stustanet/waschfreiheit/firmware/source/sensor/state_estimation.c

/*
 * Copyright 2018 Daniel Frejek
 * This source code is licensed under the MIT license that can be found
 * in the LICENSE file.
 */


#include "state_estimation.h"

#include <string.h>

#include "debug_assert.h"

static bool check_config(const state_estimation_params_t *params)
{
	for (uint8_t i = 0; i < SE_STATECOUNT; i++)
	{
		if (params->state_filter.window_sizes[i] > SE_MAX_WINDOW_SIZE ||
			params->state_filter.window_sizes[i] == 0)
		{
			printf("Invalid stateest window size %u\n", params->state_filter.window_sizes[i]);
			return false;
		}
	}

	if (params->input_filter.num_samples == 0)
	{
		printf("Number of lowpass samples must not be zero!\n");
		return false;
	}

	return true;
}


/*
 * Update the input filter.
 * This proceses the raw ADC values and calculates the <current> input filter value from the data.
 * <current> describes the short-time average power consumption of the measured device.
 * This also increments the current filter counter.
 */
static void update_input_filter(state_estimation_data_t *data, uint16_t value)
{
	ASSERT(value < (1 << 12));

	// sacle from 12 bit to 32 bit
	uint32_t value_scaled = value << 20;

	uint32_t absval = 0;

	if (value_scaled > data->input_filter.mid)
	{
		absval = value_scaled - data->input_filter.mid;
		data->input_filter.mid += data->params.input_filter.mid_value_adjustment_speed;
	}
	else if (value_scaled < data->input_filter.mid)
	{
		absval = data->input_filter.mid - value_scaled;
		data->input_filter.mid -= data->params.input_filter.mid_value_adjustment_speed;
	}

	// sacle from 32 bit to 18 bit
	absval = absval >> 14;

	data->input_filter.counter++;
	data->input_filter.current = (data->input_filter.current * data->params.input_filter.lowpass_weight + absval) / (data->params.input_filter.lowpass_weight + 1);
}


/*
 * Calculates the number of valid elements in the current window.
 *
 * NOTE:
 * The return value assumes that the element referenced by next_free already in use
 */
static uint16_t calc_current_window_used(const state_estimation_data_t *data)
{
	if (data->state_filter.window_oldest_valid > data->state_filter.window_next_free)
	{
		// Wrap-around
		// => valid values before next free and after oldest_valid
		return (data->state_filter.window_next_free + 1) + (SE_MAX_WINDOW_SIZE - data->state_filter.window_oldest_valid);
	}
	else
	{
		// Linear
		// => valid values between next free and oldest valid
		return (data->state_filter.window_next_free - data->state_filter.window_oldest_valid) + 1;
	}
}


/*
 * Adjust the window size to the current window size as defined by the current state.
 * If an old value that contributed to the <window_sum> falls out, it is subtracted from the sum.
 * Also, this function advances the window by one so that <window_next_free> will point to the next unused element
 */
static void adjust_window_size(state_estimation_data_t *data)
{
	ASSERT(data->state_filter.current_state < SE_STATECOUNT);

	// first adjust the window size so that at least one new value fits in
	uint16_t current_wnd_size = data->params.state_filter.window_sizes[data->state_filter.current_state];
	uint16_t current_window_used = calc_current_window_used(data);

	uint16_t discard_idx = data->state_filter.window_oldest_valid;
	while (current_window_used >= current_wnd_size)
	{
		// discard value
		if (data->state_filter.window[discard_idx] & (0x8000))
		{
			// msb set -> this value was used
			// => subtract it from sum

			ASSERT(data->state_filter.window_sum >= (data->state_filter.window[discard_idx] & 0x7fff));

			data->state_filter.window_sum -= (data->state_filter.window[discard_idx] & 0x7fff);
		}

		current_window_used--;
		discard_idx = (discard_idx + 1) % SE_MAX_WINDOW_SIZE;
	}

	data->state_filter.window_oldest_valid = discard_idx;
	data->state_filter.window_next_free = (data->state_filter.window_next_free + 1) % SE_MAX_WINDOW_SIZE;

	ASSERT(data->state_filter.window_oldest_valid < SE_MAX_WINDOW_SIZE);
	ASSERT(data->state_filter.window_next_free < SE_MAX_WINDOW_SIZE);
}


/*
 * Adds the <current> input value to the window at <window_next_free> and updates the <window_sum>
 * according to the reject threshold/block filter.
 *
 * NOTE: After this function <window_next_free> will point to a used element!
 */
static void update_reject_thd_filter(state_estimation_data_t *data)
{
	// scale to 15 bit
	uint16_t currentval = data->input_filter.current >> 3;
	ASSERT(currentval < (1 << 15));

	uint16_t buffer_pos = data->state_filter.window_next_free;

	if (currentval > data->params.state_filter.reject_threshold)
	{
		/*
		 * Value is above threshold => Three possibilities
		 * I    Less than <reject_consec_count> consecutive values are above threshold
		 *      (<above_reject_counter> < <reject_consec_count>)
		 *      => Insert normally, increment <above_reject_counter>
		 * II   Exactly <reject_consec_count> consecutive values are above the threshold
		 *      => Insert and add <current> to sum (mark as used)
		 *      => Insert and add all not yet added old values to the sum (and mark all as used)
		 * III  More than <reject_consec_count> consecutive values are above the threshold
		 *      => Insert and add <current> to sum (mark as used)
		 */


		if (data->state_filter.above_reject_counter >= data->params.state_filter.reject_consec_count)
		{
			// II or III => Insert and add <current> to sum (and mark as used)
			data->state_filter.window_sum += currentval;
			data->state_filter.window[buffer_pos] = currentval | (0x8000);

			if (data->state_filter.above_reject_counter == data->params.state_filter.reject_consec_count)
			{
				// II => add all old values to sum (and mark as added)

				ASSERT(data->params.state_filter.reject_consec_count <= calc_current_window_used(data));

				for (uint16_t i = 0; i < data->params.state_filter.reject_consec_count; i++)
				{
					if (buffer_pos > 0)
					{
						buffer_pos--;
					}
					else
					{
						buffer_pos = SE_MAX_WINDOW_SIZE - 1;
					}

					// Must not be added yet
					ASSERT((data->state_filter.window[buffer_pos] & 0x8000) == 0);

					data->state_filter.window_sum += data->state_filter.window[buffer_pos];
					data->state_filter.window[buffer_pos] |= 0x8000; // mark as used (contributed to sum)
				}

				// Max value -> directly accept next value
				data->state_filter.above_reject_counter = 0xffff;
			}
			return;
		}
		else
		{
			// I => only increment counter
			data->state_filter.above_reject_counter++;
		}
	}
	else
	{
		/*
		 * Value is below threshold
		 * => Only need to reset the counter
		 */
		data->state_filter.above_reject_counter = 0;
	}

	// add 15 bit scaled value (without "contributed" tag)
	data->state_filter.window[buffer_pos] = currentval;
}


/*
 * Updates / changes the current state according to the transition matrix and the old state
 * Also check the end state timer.
 */
static void do_state_transition(state_estimation_data_t *data)
{
	ASSERT(data->state_filter.current_state < SE_STATECOUNT);

	/*
	 * This is the offset of the state transition values for the current state
	 */
	uint8_t row_offset = data->state_filter.current_state * (SE_STATECOUNT - 1);

	int16_t average = stateest_get_current_rf_value(data);

	ASSERT(average >= 0);


	for (uint8_t i = 0; i < SE_STATECOUNT; i++)
	{
		uint16_t lookup_idx;

		if (i < data->state_filter.current_state)
		{
			// Index < current -> lookup at i
			lookup_idx = i;
		}
		else if(data->state_filter.current_state == i)
		{
			// i is current state -> skip this, this column does not exist in the matrix
			continue;
		}
		else
		{
			// after the current state, look up at i - 1
			lookup_idx = i - 1;
		}

		int16_t v = data->params.state_filter.transition_matrix[row_offset + lookup_idx];

		if (v < 0)
		{
			// Switch to state i, if average < -v
			if (average < -v)
			{
				data->state_filter.current_state = i;
				break;
			}
		}
		else if (v > 0)
		{
			// Switch to state i, if average > v
			if (average > v)
			{
				data->state_filter.current_state = i;
				break;
			}
		}
	}

	// finally check max time condition for end state
	if (data->state_filter.current_state == SE_STATE_END)
	{
		data->state_filter.end_state_timer++;
		if (data->state_filter.end_state_timer > data->state_filter.max_end_state_time)
		{
			// Too long in end state => switch to OFF
			data->state_filter.end_state_timer = 0;
			data->state_filter.current_state = SE_STATE_OFF;
		}
	}
	else
	{
		data->state_filter.end_state_timer = 0;
	}
}


static void update_state_filter(state_estimation_data_t *data)
{
	adjust_window_size(data);
	update_reject_thd_filter(data);
	do_state_transition(data);
}


int stateest_init(state_estimation_data_t *data, const state_estimation_params_t *params, uint16_t adc_samples_per_sec)
{
	if (!check_config(params))
	{
		return 1;
	}

	// init data
	memcpy(&(data->params), params, sizeof(data->params));
	data->input_filter.mid = SE_INITIAL_MID_VALUE;
	data->input_filter.current = 0;
	data->input_filter.counter = 0;

	memset(data->state_filter.window, 0, sizeof(data->state_filter.window));
	data->state_filter.window_next_free = 0;
	data->state_filter.window_oldest_valid = 0;
	data->state_filter.end_state_timer = 0;
	data->state_filter.max_end_state_time = (uint16_t)(((uint32_t)SE_MAX_END_STATE_TIME) * adc_samples_per_sec / params->input_filter.num_samples);
	data->state_filter.above_reject_counter = 0;
	data->state_filter.window_sum = 0;
	data->state_filter.current_state = SE_STATE_OFF;

	stateest_set_adc_sps(data, adc_samples_per_sec);

	return 0;
}


void stateest_set_adc_sps(state_estimation_data_t *data, uint16_t adc_samples_per_sec)
{
	if (data->params.input_filter.num_samples == 0)
	{
		// not initialized
		return;
	}

	data->state_filter.end_state_timer = 0;
	data->state_filter.max_end_state_time = (uint16_t)(((uint32_t)SE_MAX_END_STATE_TIME) * adc_samples_per_sec / data->params.input_filter.num_samples);
}


state_update_result_t stateest_update(state_estimation_data_t *data, uint16_t raw_value)
{
	// First update the input filter
	update_input_filter(data, raw_value);

	if (data->input_filter.counter >= data->params.input_filter.num_samples)
	{
		// if <num_samples> valuess processed, update the state filter

		data->input_filter.counter = 0;

		// rememebr if the last state was an ON state
		uint8_t was_on = (data->state_filter.current_state >= SE_STATE_ON_THRESHOLD);

		// update the state
		update_state_filter(data);

		// was_on != is_on => notify caller
		if (was_on != (data->state_filter.current_state >= SE_STATE_ON_THRESHOLD))
		{
			if (was_on)
			{
				return state_update_changed_to_off;
			}
			return state_update_changed_to_on;
		}
	}

	// no frame or on state unchanged
	return state_update_unchanged;
}


uint32_t stateest_get_frame(const state_estimation_data_t *data)
{
	if (data->input_filter.counter == 0)
	{
		return data->input_filter.current >> 2;
	}
	else
	{
		return 0xffffffff;
	}
}


int16_t stateest_get_current_rf_value(const state_estimation_data_t *data)
{
	ASSERT(data->state_filter.current_state < SE_STATECOUNT);
	return data->state_filter.window_sum / calc_current_window_used(data);
}


bool stateest_check_config(const state_estimation_data_t *data)
{
	return check_config(&(data->params));
}
