stustanet/waschfreiheit/firmware/include/messagetypes.h

/*
 * Copyright 2018 Daniel Frejek
 * This source code is licensed under the MIT license that can be found
 * in the LICENSE file.
 */


/*
 * Structure definitions of the network messages.
 * The auth structures are defined in the auth module, the handshake
 * messages here only work as headers for the "real" handshake.
 */

#pragma once

#include <stdint.h>
#include <meshnw.h>
#include "state_estimation_params.h"

/*
 * Standard ACK codes
 * The ACK code is command specific, however, if the code is used to report an error,
 * the following codes sould be used.
 */
#define ACK_OK            0 /* OK */
#define ACK_WRONGSIZE     1 /* Unexpected message size */
#define ACK_BADINDEX      2 /* A specified channel index parameter is outside of the allowed range */
#define ACK_BADPARAM      3 /* Invalid (non-index) parameter */
#define ACK_NOTSUP        4 /* Unsupported action */
#define ACK_BADSTATE      5 /* Command rejected because of the current state */
#define ACK_RETRANSMIT 0x80 /* MSB is always set if the ack was sent twice */


typedef uint8_t msg_type_t;

/*
 * Part 1 of the auth handshake
 * master -> slave
 *
 * When this is sent by the master node, this also contains a temporary route
 * to the master node.
 *
 * NOTE: Anyone can send a valid HS1 even without knowing the key so this message
 *       should not change any configuration.
 */
#define MSG_TYPE_AUTH_HS_1                  1
typedef struct
{
	msg_type_t type;
	// The next hop used for the handshake reply
	nodeid_t reply_route;
} __attribute__((packed)) msg_auth_hs_1_t;


/*
 * Part 2 of the auth handshake
 * slave -> master
 * The HS2 is signed so the information from this message can be trusted.
 *
 * Some basic status information is packed into the hs2 message to reduce the overhead of a reconnect.
 */
#define MSG_TYPE_AUTH_HS_2                  2

#define MSG_HS_2_STATUS_ROUTES 1 /* [sensor -> master] Routes OK */
#define MSG_HS_2_STATUS_SENSOR 2 /* [sensor -> master] Sensors active */
typedef struct
{
	msg_type_t type;

	// Node status (MSG_HS_2_STATUS_*)
	uint8_t status;

	// Sensor channels with a high measurement
	uint16_t channels;
} __attribute__((packed)) msg_auth_hs_2_t;


/*
 * ACK packet for authenticated packets.
 * Only the slave of a connection sends ACK
 * result_code is a command-defined result value,
 *   if the msb is set, this is an retransmission-ack
 */
#define MSG_TYPE_AUTH_ACK                   3
typedef struct
{
	msg_type_t type;
	uint8_t result_code;
} __attribute__((packed)) msg_auth_ack_t;


/*
 * Clear all current routes and resets the node's state.
 * This is the first message expected by a node after the handshake.
 * This message must at least contain a route to the master.
 */
#define MSG_TYPE_ROUTE_RESET                4

/*
 * Just like ROUTE_RESET but old routes are kept
 */
#define MSG_TYPE_ROUTE_APPEND               5

/*
 * Data for both types of route messages.
 */
typedef struct
{
	msg_type_t type;
	// The next hop used for the handshake reply
	struct
	{
		nodeid_t dst;
		nodeid_t next;
	} r[1]; // at least one route, an empty table would make no sense
} __attribute__((packed)) msg_route_data_t;


/*
 * Configures a sensor channel
 */
#define MSG_TYPE_CONFIGURE_SENSOR_CHANNEL   6
typedef struct
{
	msg_type_t type;
	uint8_t channel_id;
	state_estimation_params_t params;
} __attribute__((packed)) msg_configure_sensor_t;


/*
 * Command to the node to establish the status connection and activate the sensors.
 * The sensor configuration can still be changed after activation.
 *
 * status_retransmission_delay_* are the times (in seconds) before a status message
 * is re-send if no ack arrived. The actual delay increases linear with the number of retries.
 * For every 3 failed attempts, the current delay is increased by the base value.
 * If no ack arrived after 100 retries, the network is assumed dead and
 * the node reboots. (Needs to be reconfigured)
 */
#define MSG_TYPE_START_SENSOR               7
typedef struct
{
	msg_type_t type;
	uint8_t status_retransmission_delay;
	uint16_t active_sensors;
	uint16_t adc_samples_per_sec;
} __attribute__((packed)) msg_start_sensor_t;


/*
 * Requests a sensor node to begin transmitting raw frame values.
 * This is intended for remote sensor value calibration.
 *
 * NOTE: This causes a very high network load.
 *       If the framerate is too high, collisions due to forwarding
 *       form intermediate hops will occure.
 */
#define MSG_TYPE_BEGIN_SEND_RAW_FRAMES      8
typedef struct
{
	msg_type_t type;
	uint8_t channel;
	uint16_t num_of_frames;
} __attribute__((packed)) msg_begin_send_raw_frames_t;


/*
 * Requests the raw status values from a sensor.
 * This is intended for debug only as the result
 * is sent unauthenticated.
 */
#define MSG_TYPE_GET_RAW_STATUS                   9
typedef struct
{
	msg_type_t type;
} __attribute__((packed)) msg_get_raw_status_t;


/*
 * No operation, this is used by the master to check if a node is still alive
 * NOTE: Unlike the echo request, this packet is sent through the authenticated channel,
 *       so that no one can fake the reply.
 */
#define MSG_TYPE_NOP                        10
typedef struct
{
	msg_type_t type;
} __attribute__((packed)) msg_nop_t;


/*
 * Sets the status LEDs an a node
 * The color is encoded into 4 bits per LED. The resulting color is defined by the colortable.
 */
#define MSG_TYPE_LED                        11
typedef struct
{
	msg_type_t type;
	uint8_t data[0];
} __attribute__((packed)) msg_led_t;

/*
 * Tell the node to reset and rebuild the status channel.
 * If the master is reset and the node is not, the status channel
 * context of the node is invalid and needs to be reinitialized.
 */
#define MSG_TYPE_REBUILD_STATUS_CHANNEL     12
typedef struct
{
    msg_type_t type;
} __attribute__((packed)) msg_rebuild_status_channel_t;


/*
 * Configure an LED to blink on a status change.
 * The number of channels to configure is defined by the message size.
 * The idea is that the LED starts to blink when the change occures to signal
 * a status change is being processed by the system. When the change message arrives
 * at the master, it will send a LED color command which will reset the blink status.
 */
#define MSG_TYPE_CONFIGURE_STATUS_CHANGE_INDICATOR     13
typedef struct
{
	msg_type_t type;
	struct
	{
		uint8_t led;
		uint8_t color : 4;
		uint8_t channel : 4;
	} __attribute__((packed)) data[0];
} __attribute__((packed)) msg_configure_status_change_indicator_t;


/*
 * Configures an auxiliary (sensor) channel for frequency detection.
 * This channel measures the frequency on an input and checks if this freq is above a threshold.
 * AUX channel handled like sensor channels,
 * they need to be enabled by the START_SENSOR command and
 * send status changes through the STATUS_UPDATE.
 * These channels are used for special hardware like a frequency counter.
 * These 'special' channels are implemented on demand,
 * so which AUX channels are available is defined by the specific sensor node.
 */
#define MSG_TYPE_CONFIGURE_FREQ_CHANNEL   14
typedef struct
{
	msg_type_t type;

	// Channel id to configure
	// Frequency channels start after the normal channels
	uint8_t channel_id;

	// Minimum frequency in edges per sample
	// The sample time is define in the freq channel implementation
	uint16_t threshold;

	// If more than <negative_threshold> samples of the last <sample_count> samples are negative,
	// the status is changed to 0.
	uint8_t sample_count;
	uint8_t negative_threshold;
} __attribute__((packed)) msg_configure_freq_channel_t;


/*
 * Request information about the connected storage and configures the logger.
 * The node will change the logger config and respond with an unauthenticated MSG_TYPE_STORAGE_STATUS message.
 */
#define MSG_TYPE_STORAGE_CTL 15

// Don't change any config
// arg is ignored
#define STORAGE_CTL_REQ_TYPE_NOP      0x00

// Close the logfile
// arg is ignored
#define STORAGE_CTL_REQ_TYPE_CLOSE    0x01

// Set a new log file
// arg is the filename
#define STORAGE_CTL_REQ_TYPE_SET_FILE_OVERWRITE 0x02
#define STORAGE_CTL_REQ_TYPE_SET_FILE_APPEND    0x03

// arg is the mark string
#define STORAGE_CTL_REQ_TYPE_MARK     0x04

// If this bit is set in the request field, this command will change
// the bits of the logger group specified in the lower bits of the request.
// In this case the arg is a 32 bit integer, that defines the parameter to set the logger group to.
#define STORAGE_CTL_REQ_TYPE_GROUP 0x80
typedef struct
{
	msg_type_t type;

	uint8_t request;

	uint8_t arg[0];
} __attribute__((packed)) msg_storage_ctl_t;


/*
 * Status update message sent by the node through the status channel to the master.
 */
#define MSG_TYPE_STATUS_UPDATE             64
typedef struct
{
	msg_type_t type;
	uint16_t status;
} __attribute__((packed)) msg_status_update_t;

// above 128 -> not signed

/*
 * Request to send an echo reply
 * NOTE: This is only intended for testing and diagnostics.
 *       To check if a node is still alive, use the NOP request.
 */
#define MSG_TYPE_ECHO_REQUEST             128
typedef struct
{
	msg_type_t type;
} __attribute__((packed)) msg_echo_request_t;

/*
 * Echo reply
 */
#define MSG_TYPE_ECHO_REPLY               129
typedef struct
{
	msg_type_t type;
} __attribute__((packed)) msg_echo_reply_t;

/*
 * Packet containing raw frame values
 */
#define MSG_TYPE_RAW_FRAME_VALUES         130
typedef struct
{
	msg_type_t type;
	uint16_t values[0];
} __attribute__((packed)) msg_raw_frame_data_t;

/*
 * Packet containing raw status information
 * The number of channels is determined by the length of the packet.
 * Each channel data is 5 bytes long.
 * The upper two bits in the last byte of the channel data
 * define the type of the channel.
 */
#define RAW_STATUS_CHANNEL_TYPE_WASCH 0x00
#define RAW_STATUS_CHANNEL_TYPE_FREQ  0x40

#define MSG_TYPE_RAW_STATUS               131
typedef struct
{
	msg_type_t type;

	// Global data
	uint32_t node_status;
	uint32_t sensor_loop_delay;
	uint32_t retransmission_counter;
	uint32_t uptime;
	uint16_t channel_status;
	uint16_t channel_enabled;
	uint8_t rt_base_delay;

	union
	{
		struct
		{
			uint16_t reserved1;
			uint16_t reserved2;
			uint8_t  type;
		} __attribute__((packed)) common;

		struct
		{
			uint16_t if_current;
			uint16_t rf_current;
			uint8_t current_status;
		} __attribute__((packed)) wasch;

		struct
		{
			uint16_t raw;
			uint16_t reserved;
			uint8_t  neg;
		} __attribute__((packed)) freq;
	} __attribute__((packed)) channels[0];

} __attribute__((packed)) msg_raw_status_t;


/*
 * Packet containing raw status information about the usb storage.
 */
#define MSG_TYPE_STORAGE_STATUS 132

#define STORAGE_STATUS_MOUNTED 1
#define STORAGE_STATUS_LOGGING_ACTIVE 2
typedef struct
{
	msg_type_t type;

	uint8_t status;

	// logger option bits
	uint32_t logger_opt_adc;
	uint32_t logger_opt_stateest;
	uint32_t logger_opt_network;

	// Free space on the USB device in MB
	uint32_t usb_free_mb;

} __attribute__((packed)) msg_storage_status_t;


typedef union
{
	msg_type_t type;
	msg_auth_hs_1_t hs1;
	msg_auth_hs_2_t hs2;
	msg_auth_ack_t ack;
	msg_route_data_t route;
	msg_configure_sensor_t scfg;
	msg_start_sensor_t ssta;
	msg_begin_send_raw_frames_t srf;
	msg_get_raw_status_t grs;
	msg_nop_t nop;
	msg_status_update_t su;
	msg_echo_request_t echo_rq;
	msg_echo_reply_t echo_rp;
	msg_raw_frame_data_t frames;
	msg_raw_status_t rs;


} __attribute__((packed)) msg_union_t;
